MatejBosansky/Neopixel-Effects-Box/docs/photos/DSC_0813.JPG

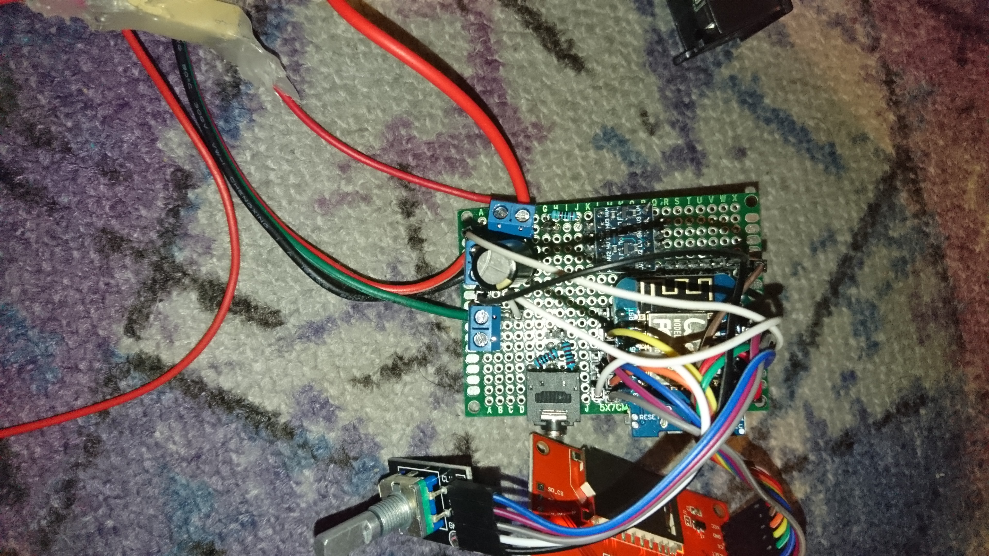
docs/photos/DSC_0813.JPG
