MatejBosansky/Neopixel-Effects-Box/docs/photos/DSC_0814.JPG

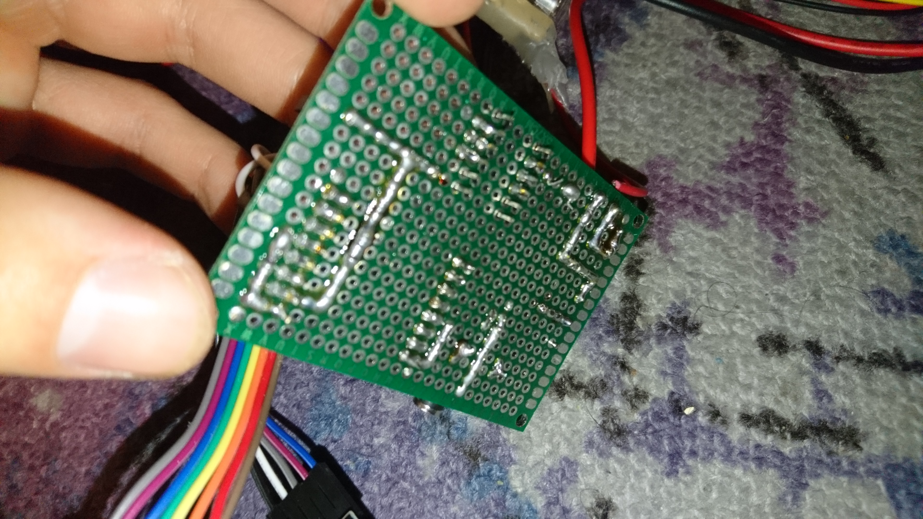
docs/photos/DSC_0814.JPG
