MatejBosansky/Neopixel-Effects-Box/docs/photos/image-20180716_223214.jpg

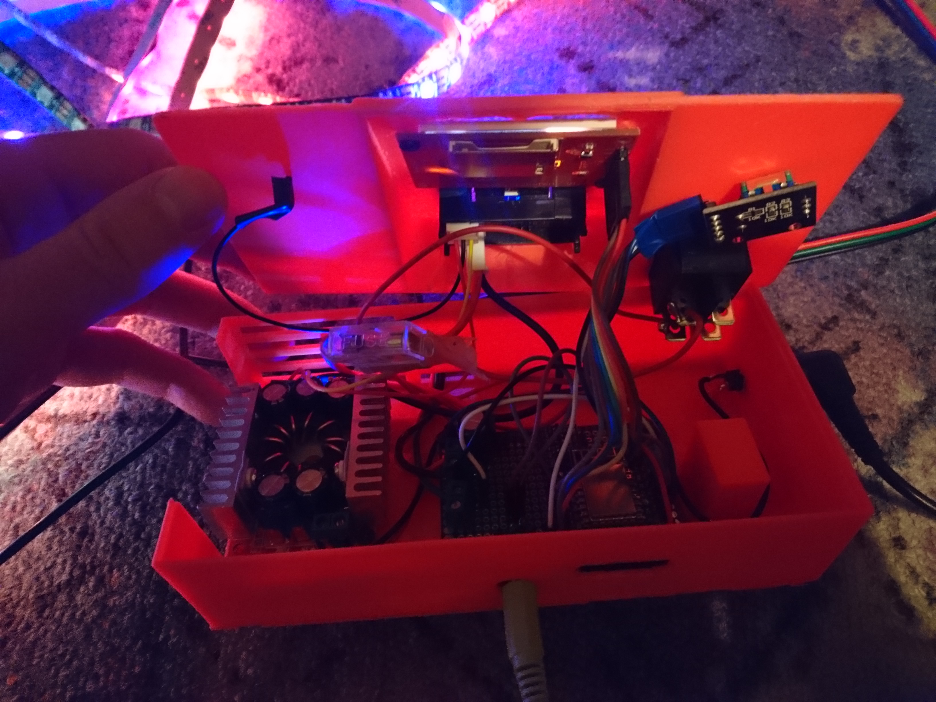
docs/photos/image-20180716_223214.jpg
